DMan0435/GAL-v2-mod-D/IMAGES/img1.jpg

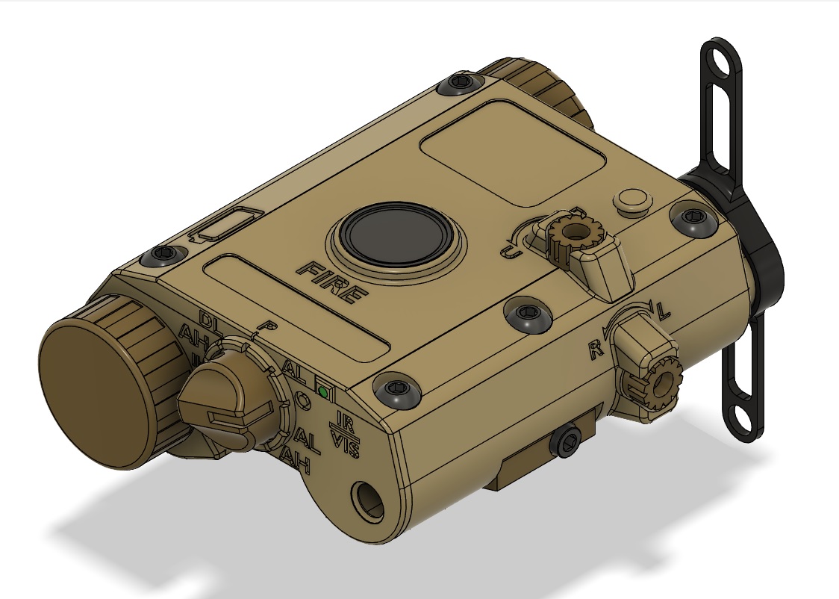
IMAGES/img1.jpg
