DMan0435/GAL-v2-mod-D/IMAGES/img2.jpg

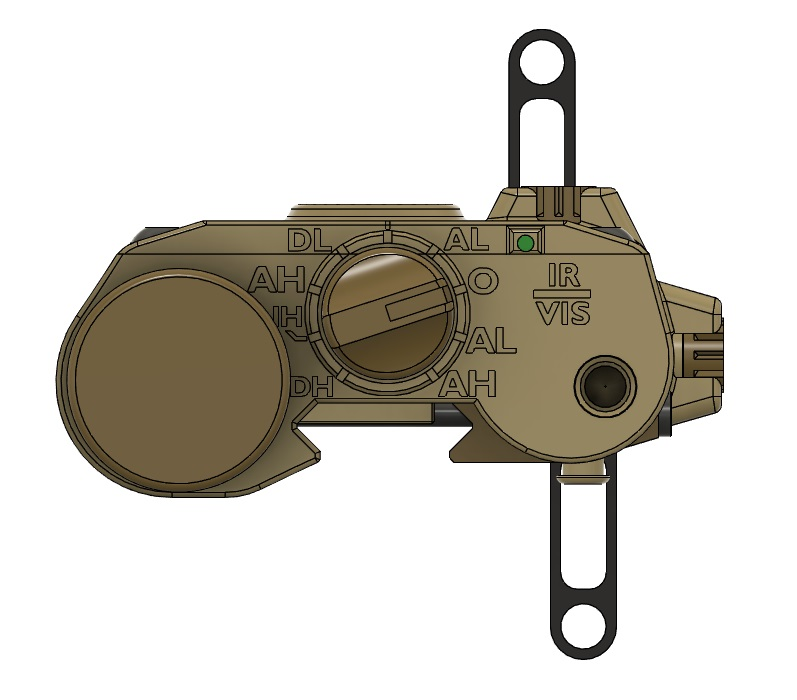
IMAGES/img2.jpg
