DMan0435/GAL-v2-mod-D/IMAGES/img10.jpg

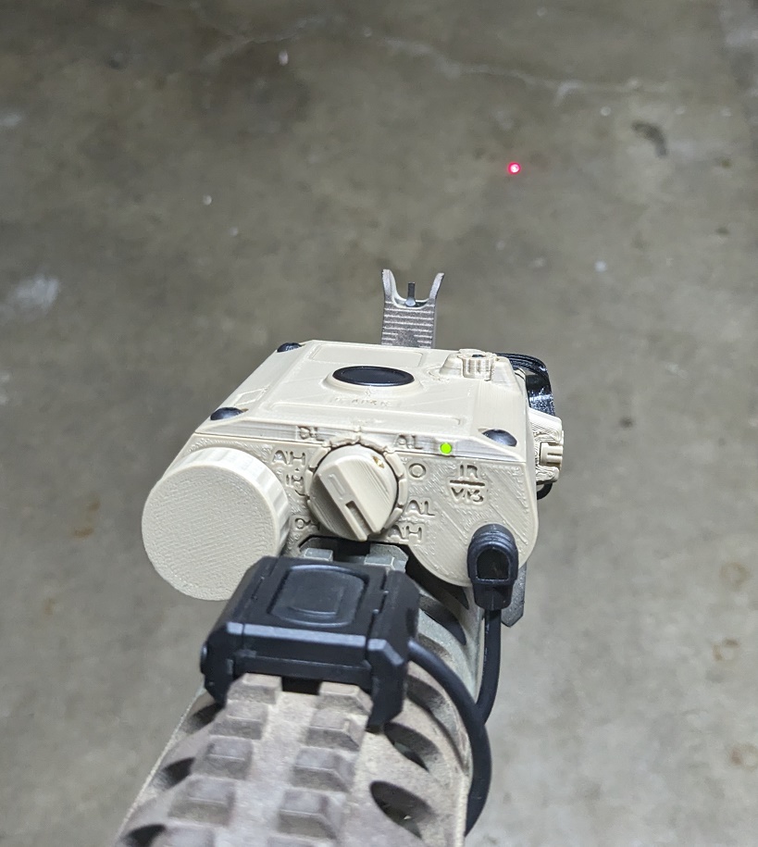
IMAGES/img10.jpg
