DMan0435/GAL-v2-mod-D/STL/GAL v2 mod D - LASER HOUSING.stl

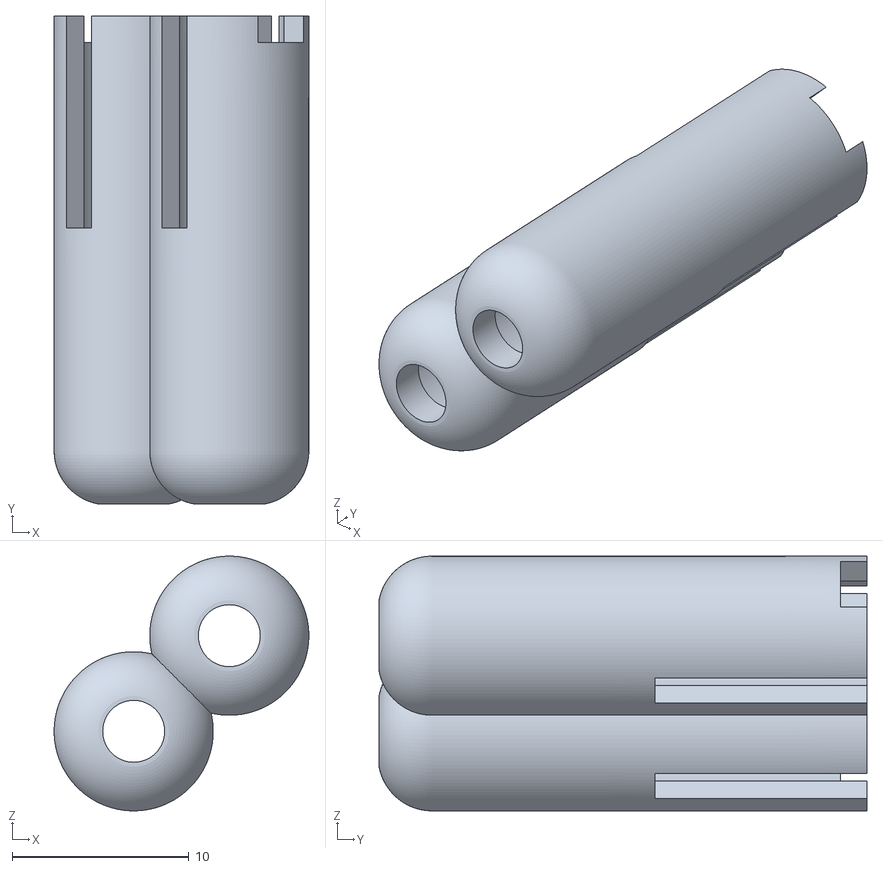
[picture p23: CAD file, 2023-11-16]
STL/GAL v2 mod D - LASER HOUSING.stl
14.4 x 27.6 x 14.4
