DMan0435/GAL-v2-mod-D/STL/GAL v2 mod D - LID (18mm Button).stl

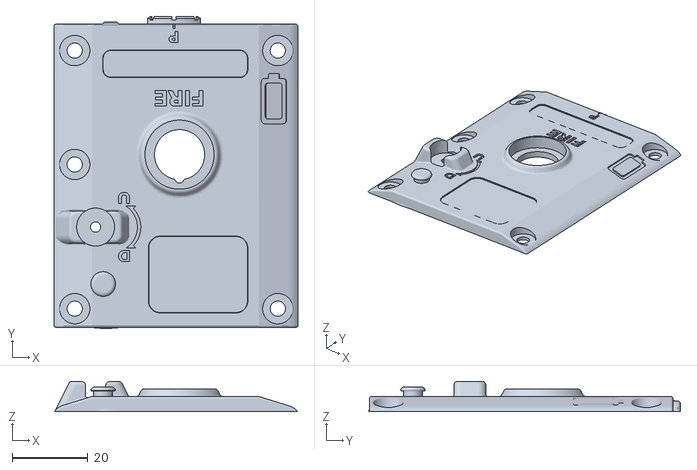
[picture p24: CAD file, 2023-11-16]
STL/GAL v2 mod D - LID (18mm Button).stl
64.3 x 82.3 x 8.00
