DMan0435/GAL-v2-mod-D/STL/GAL v2 mod D - ZERO LOCK NUT.stl

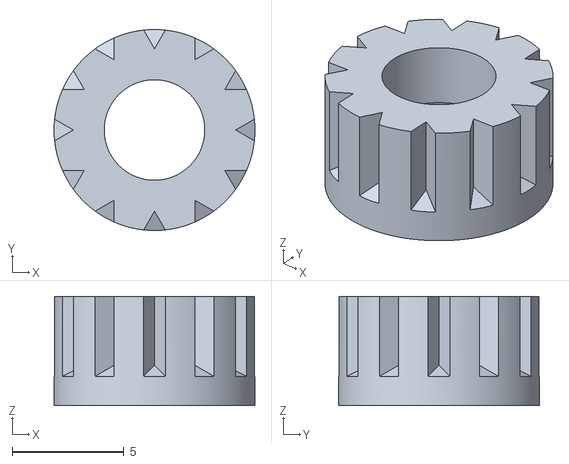
[picture p25: CAD file, 2023-11-16]
STL/GAL v2 mod D - ZERO LOCK NUT.stl
9.00 x 9.00 x 4.90
