DMan0435/GAL-v2-mod-D/PCB/Knack PCB retrofit wiring diagram.jpg

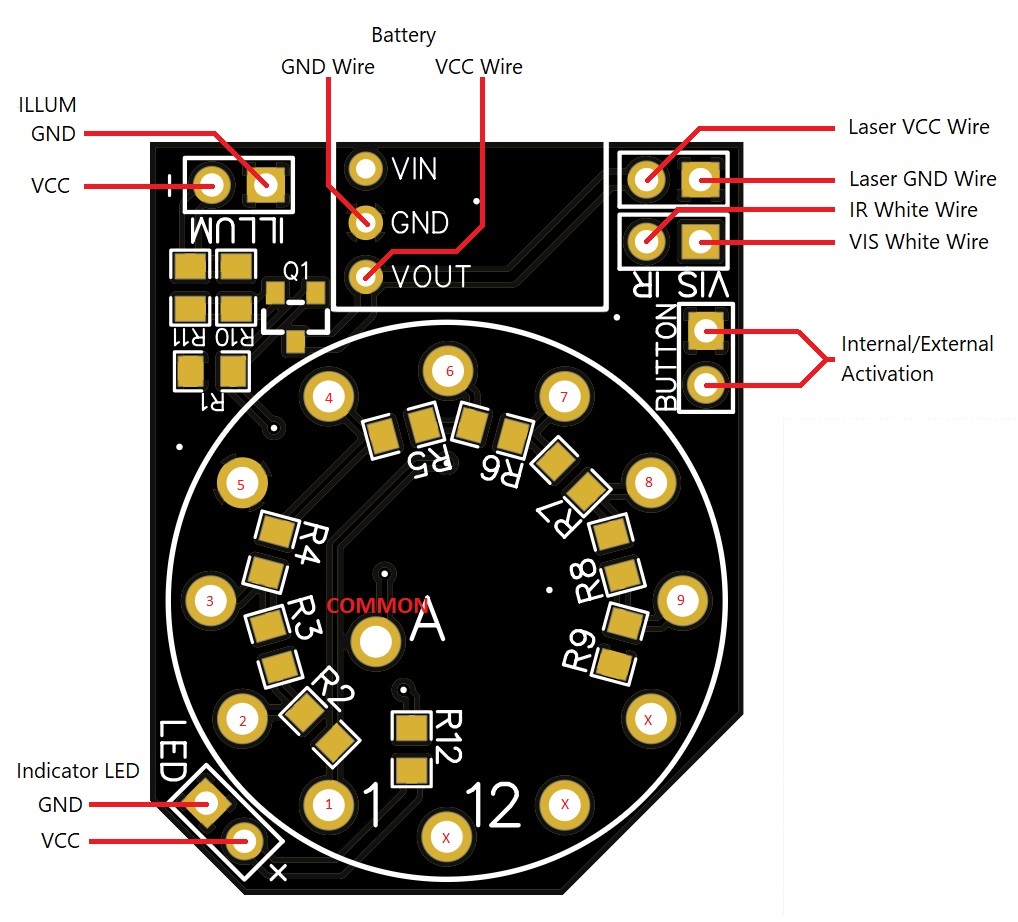
PCB/Knack PCB retrofit wiring diagram.jpg
